Splash005/eInk_Table_Reservation/pictures/Display_APMode.jpg

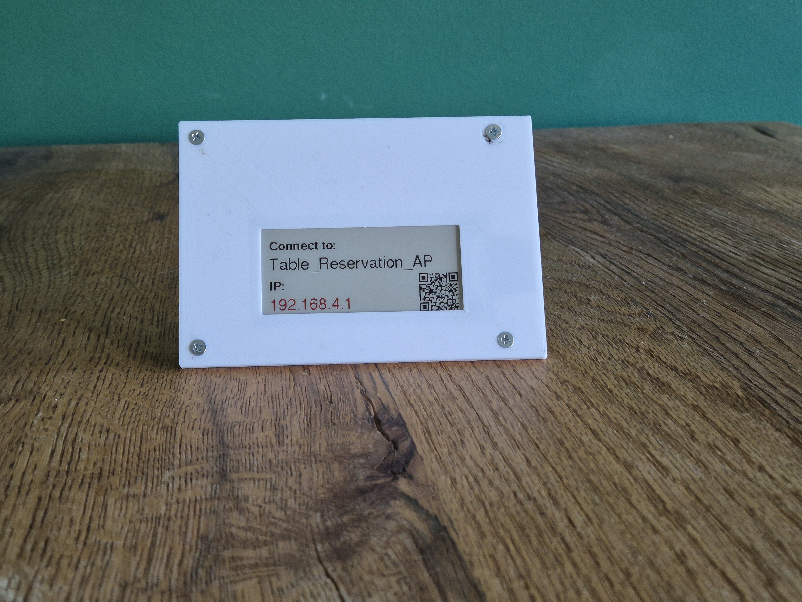
pictures/Display_APMode.jpg
