Splash005/eInk_Table_Reservation/pictures/Display_State_ACTIVE.jpg

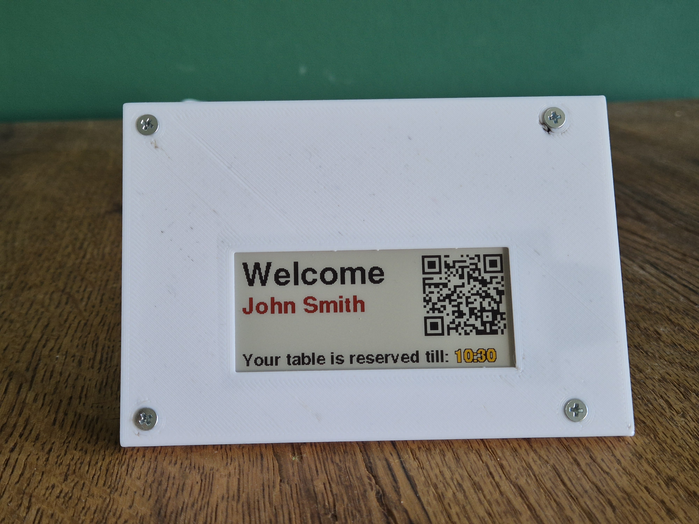
pictures/Display_State_ACTIVE.jpg
