Splash005/eInk_Table_Reservation/pictures/Display_State_UPCOMING.jpg

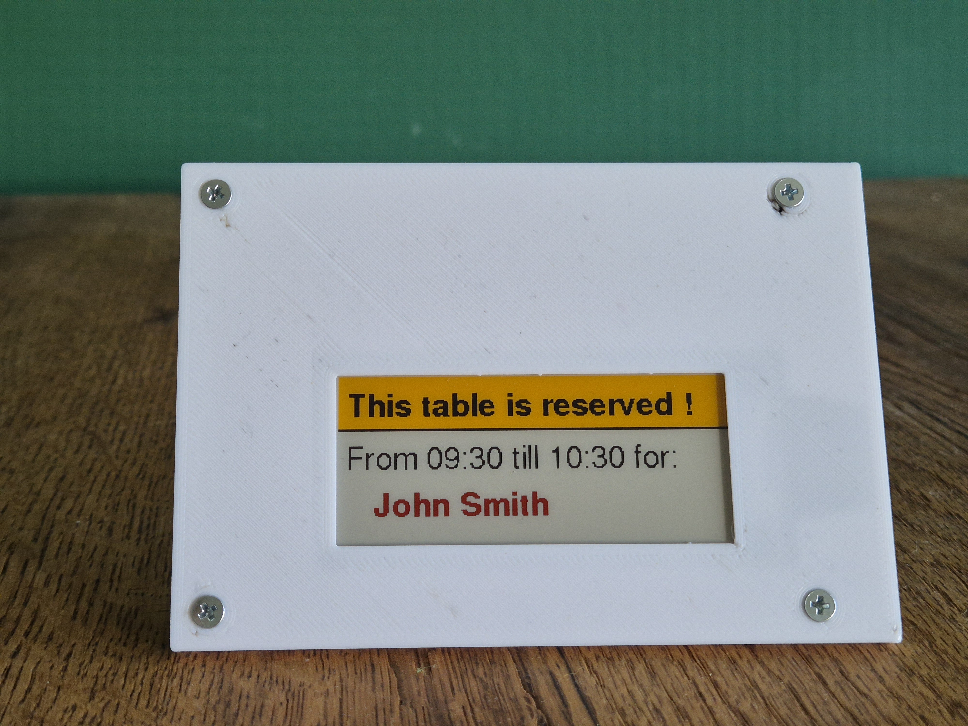
pictures/Display_State_UPCOMING.jpg
