Splash005/eInk_Table_Reservation/pictures/Reservation_TimePicker.jpg

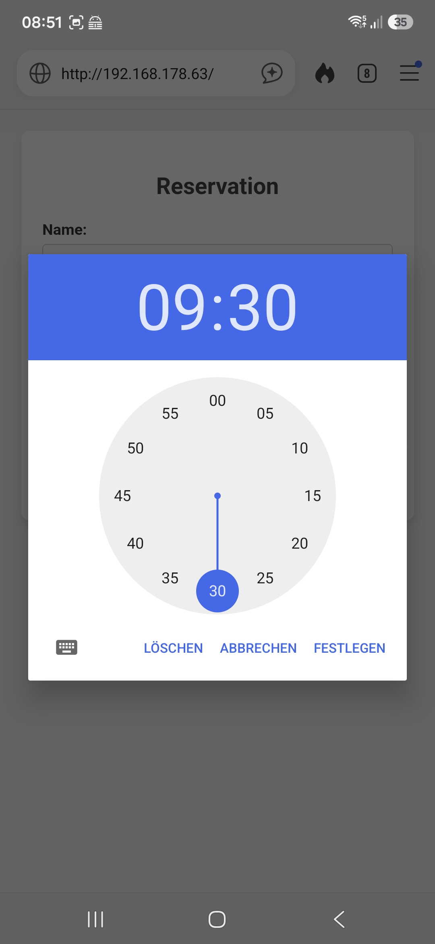
pictures/Reservation_TimePicker.jpg
